ximtech/ai-meter/Documents/ESP32-CAM-MB-S001.webp

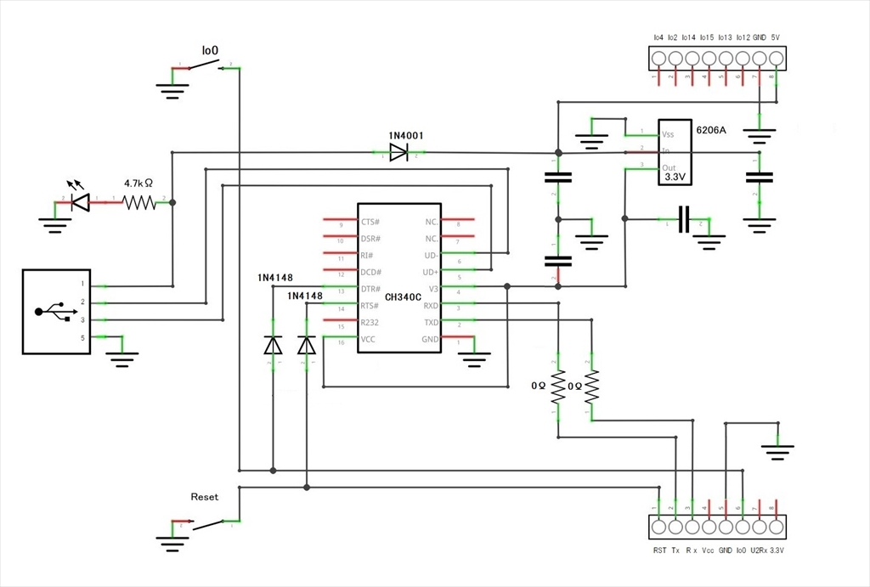
Documents/ESP32-CAM-MB-S001.webp
