ximtech/ai-meter/Images/esp32-cam.png

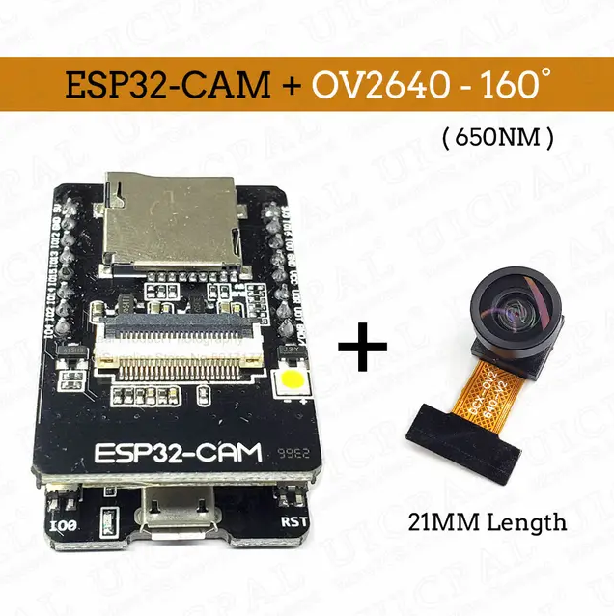
Images/esp32-cam.png
