ximtech/ai-meter/Images/green-right-arrow-600x320.png

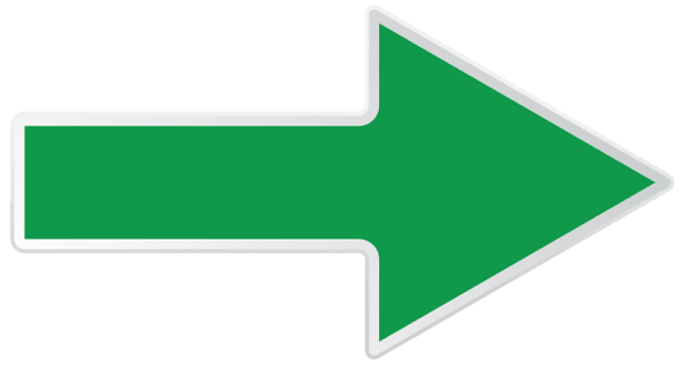
Images/green-right-arrow-600x320.png
