ximtech/ai-meter/Images/meter_photo.png

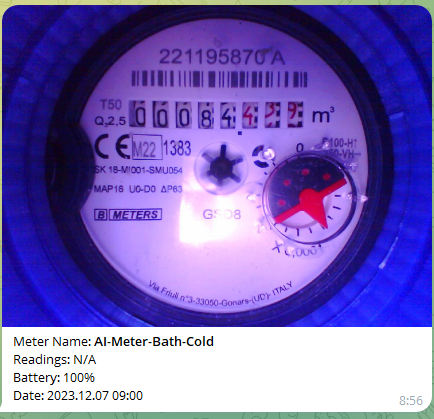
Images/meter_photo.png
